hics-nepal/hics-iesh/docs/cad/renders/drill_wall.png

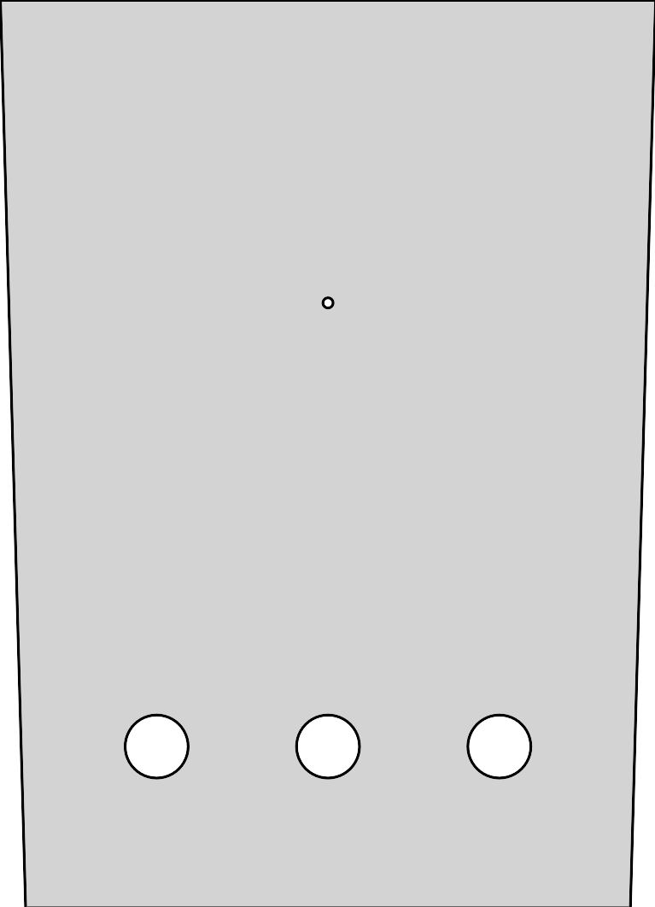
docs/cad/renders/drill_wall.png
