hics-nepal/hics-iesh/docs/reference-photos/01-circuit-as-built-cardboard.jpg

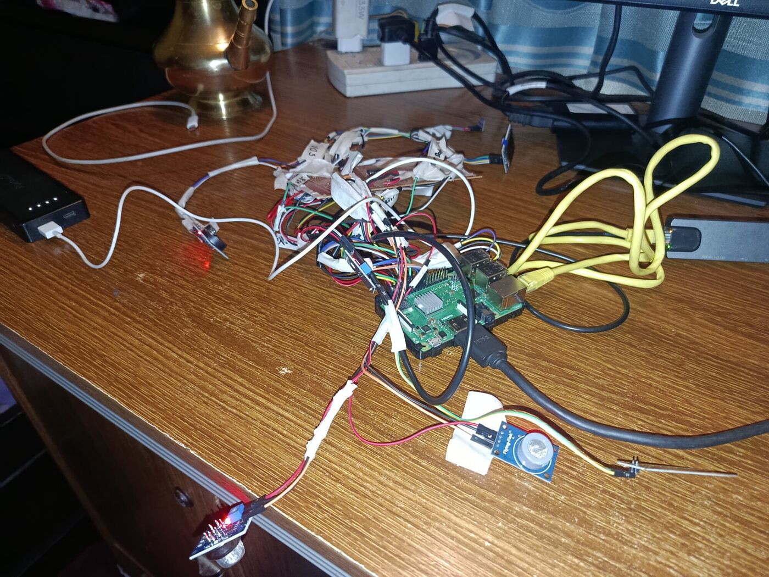
docs/reference-photos/01-circuit-as-built-cardboard.jpg
