hics-nepal/hics-iesh/curriculum/modules/activities.py

from .climate import CLIMATE
from .soil import SOIL
from .air import AIR
from .data import DATA
from .environment import ENVIRONMENT

MODULES = {
    'climate': CLIMATE,
    'soil': SOIL,
    'air': AIR,
    'data': DATA,
    'environment': ENVIRONMENT,
}
